kimberlycoston/christmas/captured_image_20250404_062548.jpg

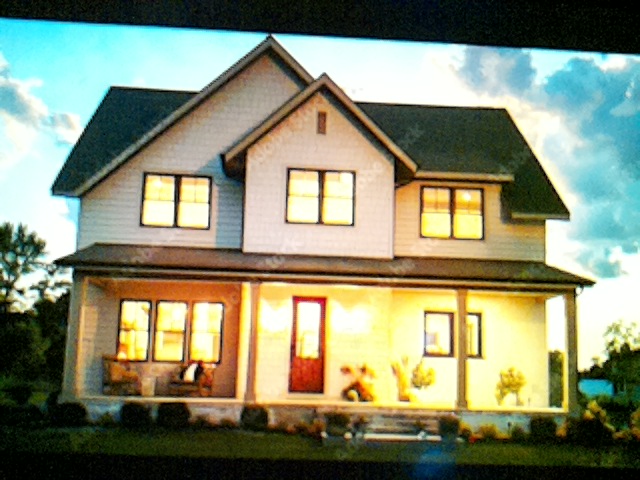
captured_image_20250404_062548.jpg
