kimberlycoston/christmas/captured_image_20250404_070609.jpg

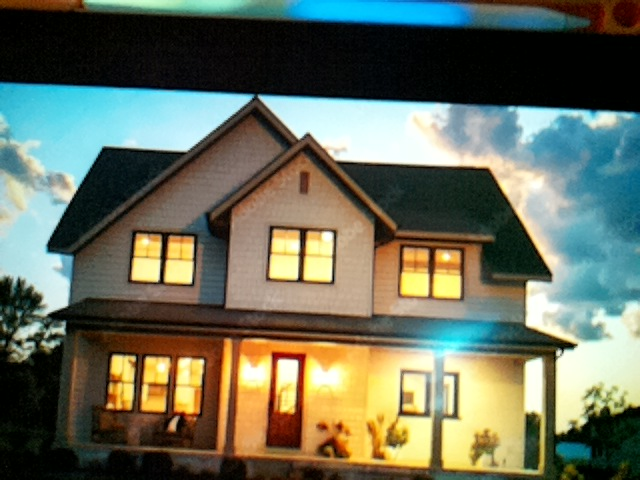
captured_image_20250404_070609.jpg
