kimberlycoston/christmas/gifs/kims.gif

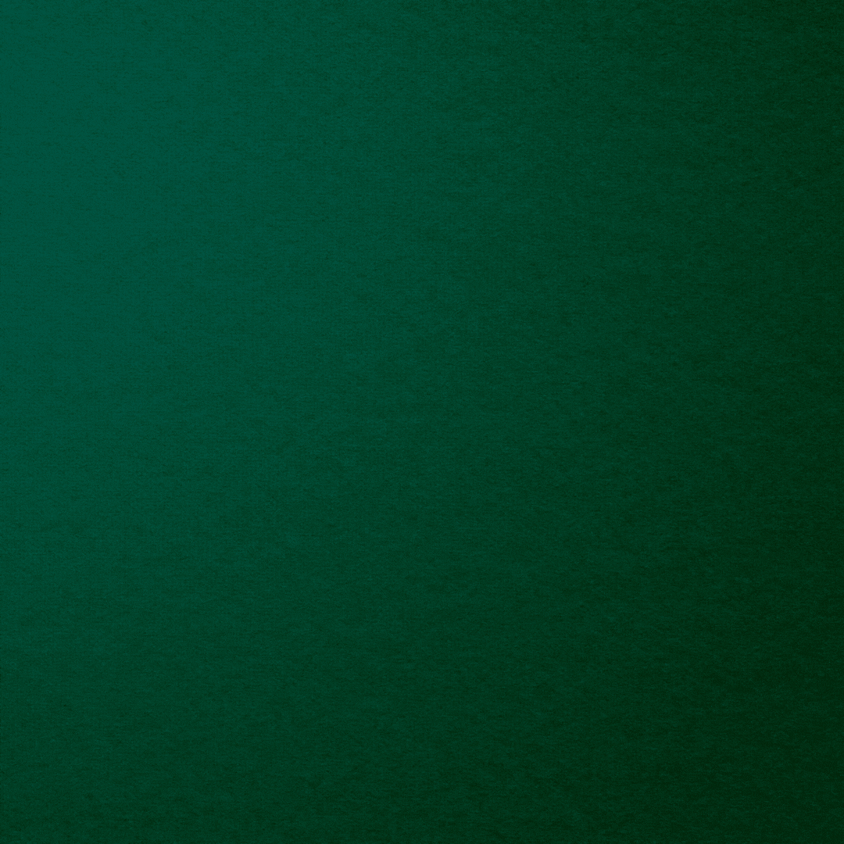
gifs/kims.gif
