kimberlycoston/christmas/backup_folder/masked_overlay_original.py

import cv2
import numpy as np
from PIL import Image
import os

# ============================
# CONFIGURATION
# ============================
mask_path = "mask_edited.png"
gif_path = "kims.gif"
output_video_path = "masked_projection_original_mom_snowflakes.mp4"
original_image_path = "mom_house.png"
fullscreen_preview = True

# ============================
# LOAD MASK
# ============================
mask = cv2.imread(mask_path, cv2.IMREAD_GRAYSCALE)
if mask is None:
    raise FileNotFoundError("Could not find mask image!")

height, width = mask.shape

# ============================
# LOAD GIF FRAMES
# ============================
gif = Image.open(gif_path)
frames = []
durations = []

try:
    while True:
        frame = gif.convert("RGB")
        frame_np = np.array(frame)
        frame_bgr = cv2.cvtColor(frame_np, cv2.COLOR_RGB2BGR)
        frame_resized = cv2.resize(frame_bgr, (width, height))
        frames.append(frame_resized)
        durations.append(gif.info.get("duration", 100))
        gif.seek(gif.tell() + 1)
except EOFError:
    pass

print(f"Loaded {len(frames)} frames from the GIF.")

# ============================
# LOAD BASE IMAGE WITH ALPHA
# ============================
base_img_pil = Image.open(original_image_path).convert("RGBA")
base_img_pil = base_img_pil.resize((width, height))
base_img = np.array(base_img_pil)

# Separate base image RGB and Alpha
base_rgb = base_img[:, :, :3]
base_alpha = base_img[:, :, 3]
_, base_alpha_mask = cv2.threshold(base_alpha, 1, 255, cv2.THRESH_BINARY)
base_alpha_mask_3ch = cv2.merge([base_alpha_mask] * 3)

# ============================
# PREPARE VIDEO OUTPUT
# ============================
fps = int(1000 / np.mean(durations))
fourcc = cv2.VideoWriter_fourcc(*"mp4v")
video_out = cv2.VideoWriter(output_video_path, fourcc, fps, (width, height))

# ============================
# CREATE MASKED ANIMATION
# ============================
mask_3ch = cv2.merge([mask, mask, mask])

for i, frame in enumerate(frames):
    masked = cv2.bitwise_and(frame, mask_3ch)
    output_frame = np.where(mask_3ch > 0, masked, base_rgb)
    output_frame = np.where(base_alpha_mask_3ch == 0, 0, output_frame)  # Use black background for transparency

    video_out.write(output_frame)

    if fullscreen_preview:
        cv2.namedWindow("Projection", cv2.WND_PROP_FULLSCREEN)
        cv2.setWindowProperty("Projection", cv2.WND_PROP_FULLSCREEN, cv2.WINDOW_FULLSCREEN)
        cv2.moveWindow("Projection", 1920, 0)
        cv2.setMouseCallback("Projection", lambda *args : None)
        cv2.setWindowProperty("Projection", cv2.WND_PROP_TOPMOST, 1)
        cv2.imshow("Projection", output_frame)
        key = cv2.waitKey(int(1000 / fps))
        if key == 27:  # ESC to stop
            break

video_out.release()
cv2.destroyAllWindows()
print(f"✅ Saved masked projection video to {output_video_path}")
